prochazkapeter/energy-monitor/src/measurement.h

#include "config.h"

String measure_data(void);
void save_date(String message, const char *location);
void print_date(const char *location);
time_t read_date(const char *date);
void project_energy(void);
void reset_energy(void);
